glaukon-ariston/chest-of-drawers-bookcase/artifacts/export/stl/PedestalSide.stl

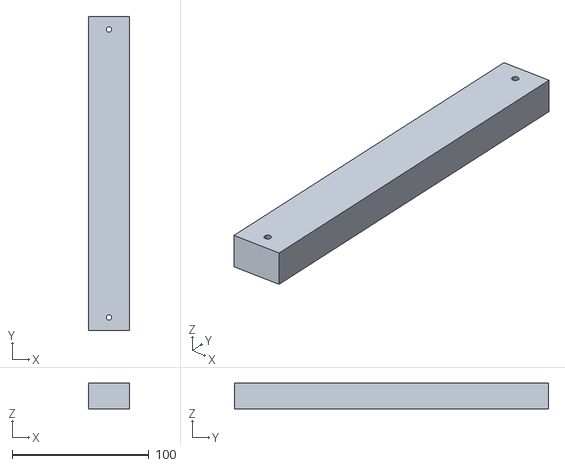
[picture p14: CAD file, 2025-08-23]
artifacts/export/stl/PedestalSide.stl
30.0 x 230.0 x 19.0
