glaukon-ariston/chest-of-drawers-bookcase/artifacts/export/stl/DrawerBottom.stl

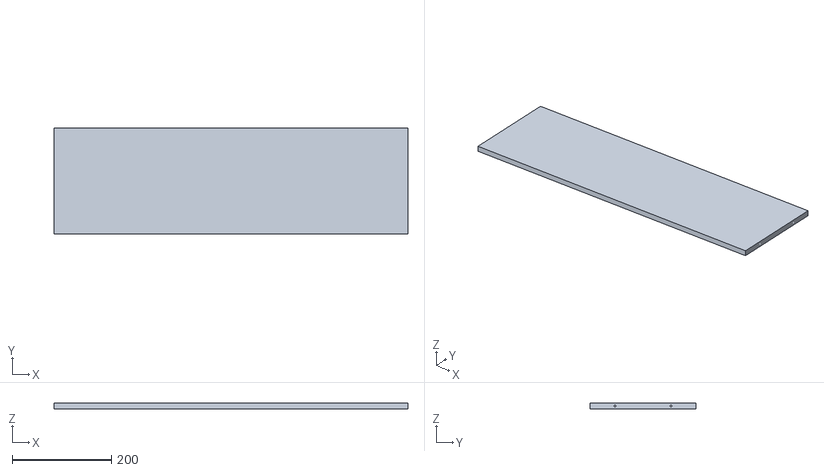
[picture p15: CAD file, 2025-08-23]
artifacts/export/stl/DrawerBottom.stl
712.0 x 213.0 x 12.0
