glaukon-ariston/chest-of-drawers-bookcase/artifacts/export/stl/PedestalFrontBack.stl

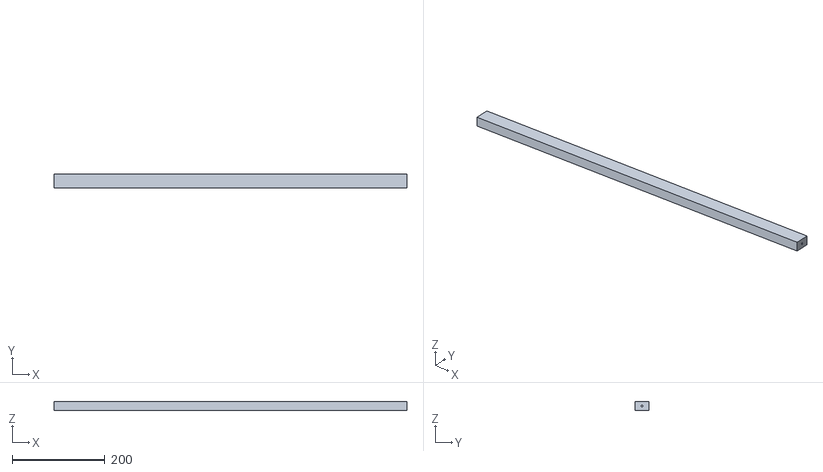
[picture p16: CAD file, 2025-08-23]
artifacts/export/stl/PedestalFrontBack.stl
762.0 x 30.0 x 19.0
