glaukon-ariston/chest-of-drawers-bookcase/artifacts/export/stl/DrawerFrontStandard.stl

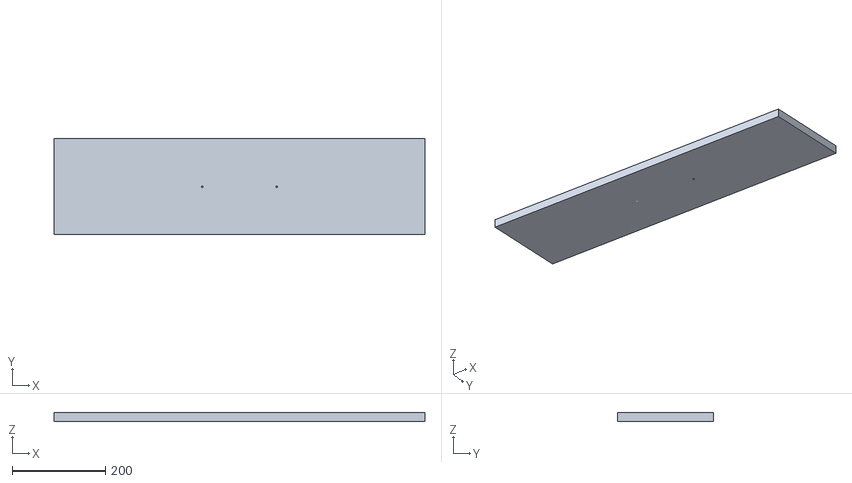
[picture p17: CAD file, 2025-08-23]
artifacts/export/stl/DrawerFrontStandard.stl
797.0 x 207.0 x 19.0
